hiulit/Murtop-Raspberry-Pi-Bartop-Arcade-Machine-Project/assets/images/GPIO-Adaftuit-retrogame.png

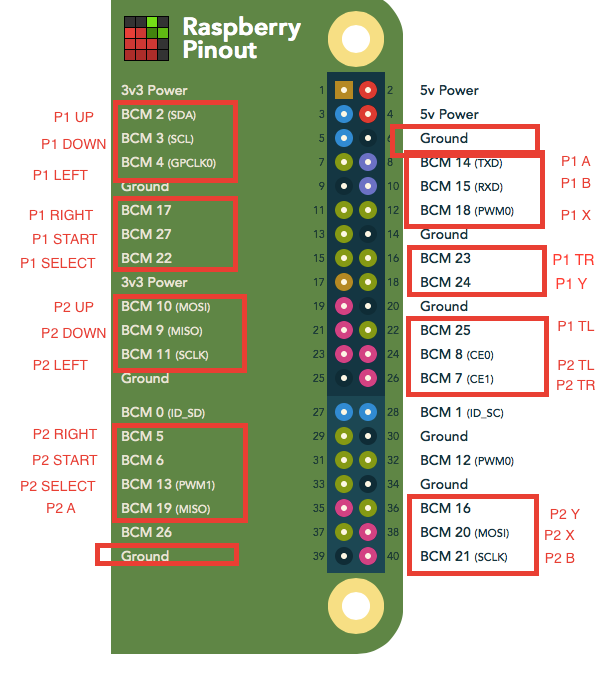
assets/images/GPIO-Adaftuit-retrogame.png
