hiulit/Murtop-Raspberry-Pi-Bartop-Arcade-Machine-Project/assets/images/wood-work-11.jpg

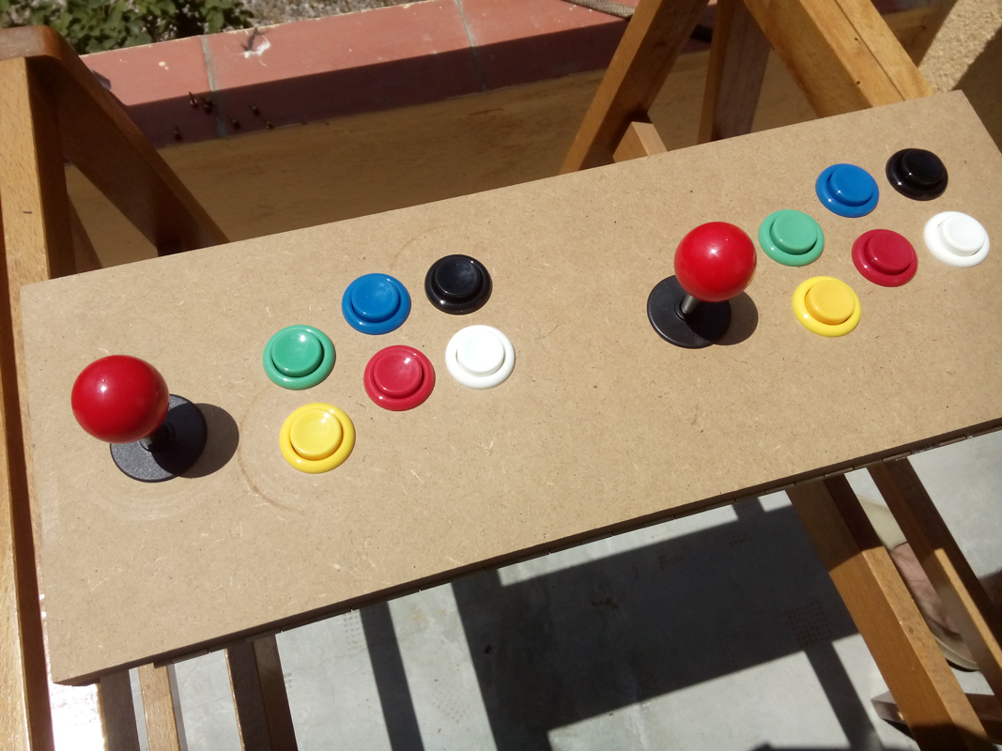
assets/images/wood-work-11.jpg
