hiulit/Murtop-Raspberry-Pi-Bartop-Arcade-Machine-Project/assets/images/wood-work-22.jpg

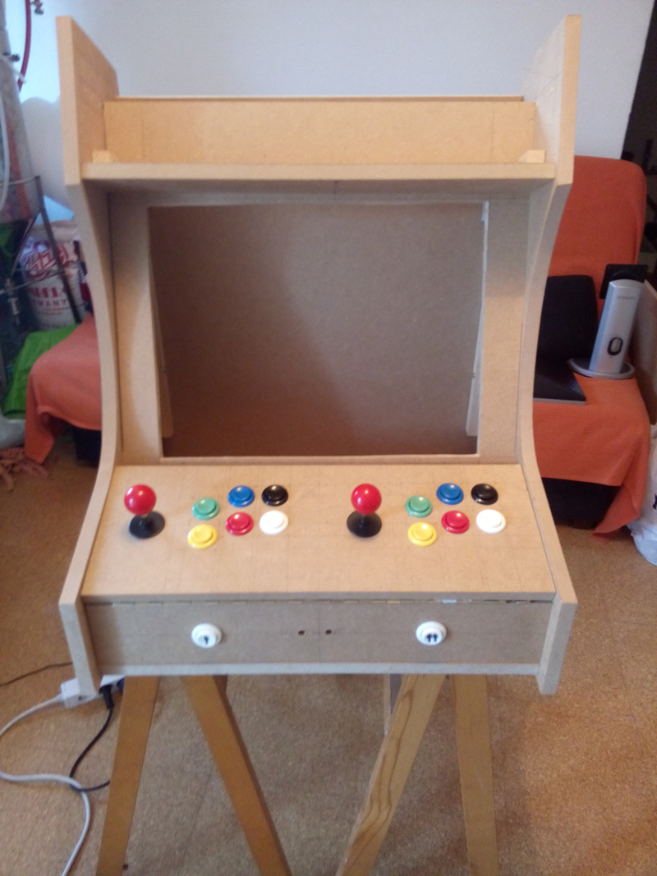
assets/images/wood-work-22.jpg
