hiulit/Murtop-Raspberry-Pi-Bartop-Arcade-Machine-Project/assets/images/wood-work-23.jpg

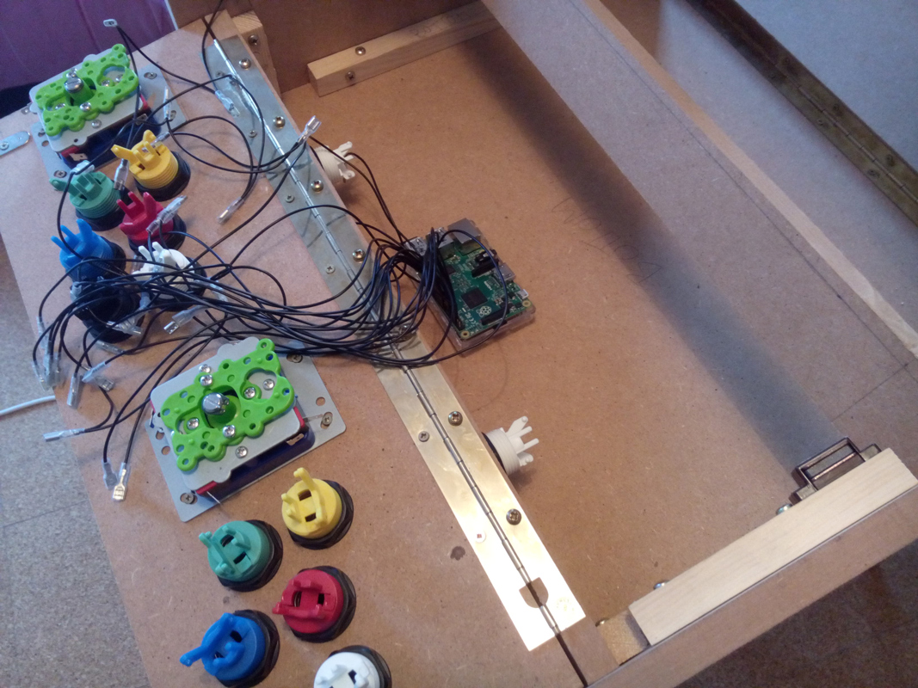
assets/images/wood-work-23.jpg
