hiulit/Murtop-Raspberry-Pi-Bartop-Arcade-Machine-Project/assets/images/wood-work-26.jpg

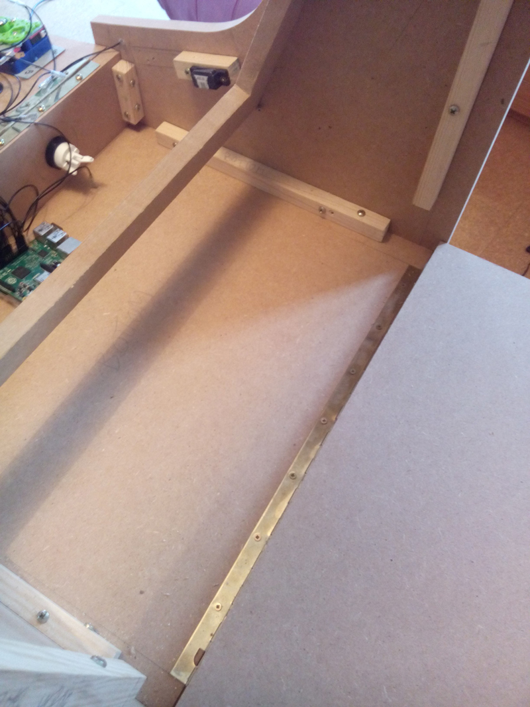
assets/images/wood-work-26.jpg
