hiulit/Murtop-Raspberry-Pi-Bartop-Arcade-Machine-Project/assets/images/wood-work-32.jpg

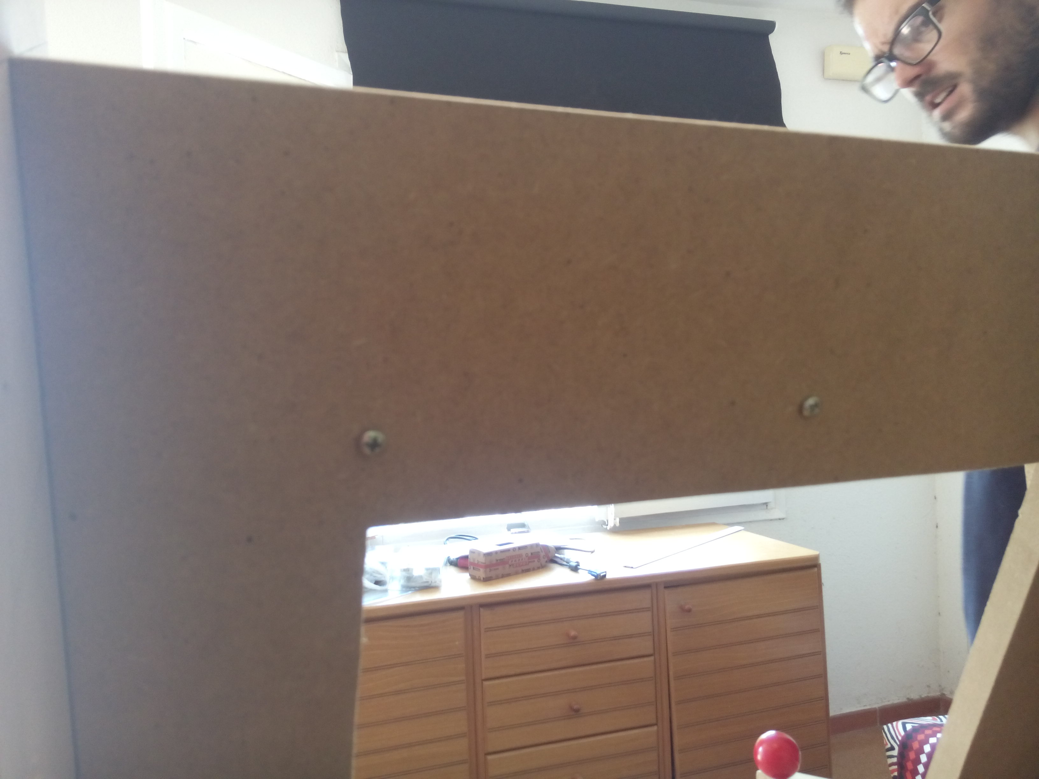
assets/images/wood-work-32.jpg
