hiulit/Murtop-Raspberry-Pi-Bartop-Arcade-Machine-Project/assets/images/wood-work-37.jpg

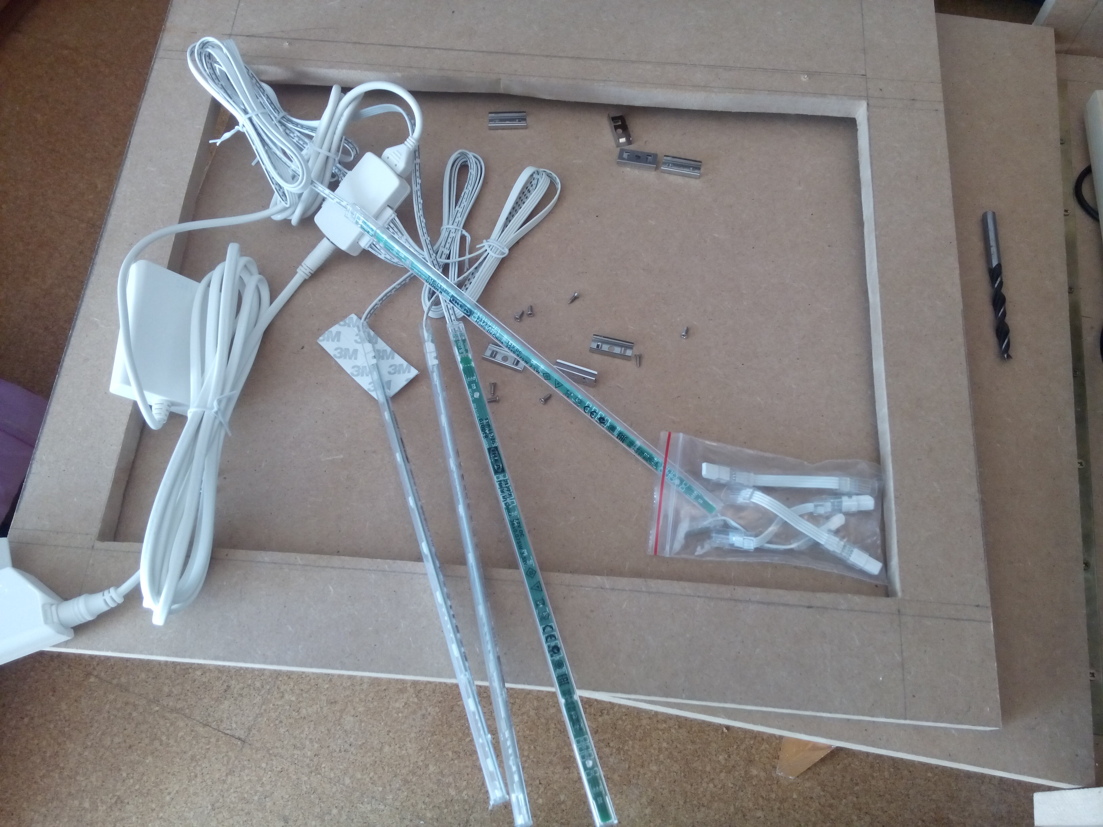
assets/images/wood-work-37.jpg
