hiulit/Murtop-Raspberry-Pi-Bartop-Arcade-Machine-Project/assets/images/wood-work-38.jpg

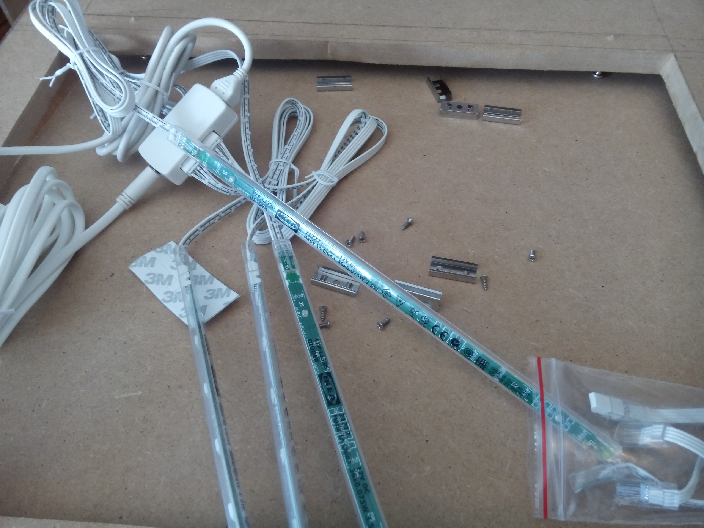
assets/images/wood-work-38.jpg
