hiulit/Murtop-Raspberry-Pi-Bartop-Arcade-Machine-Project/assets/images/wood-work-41.jpg

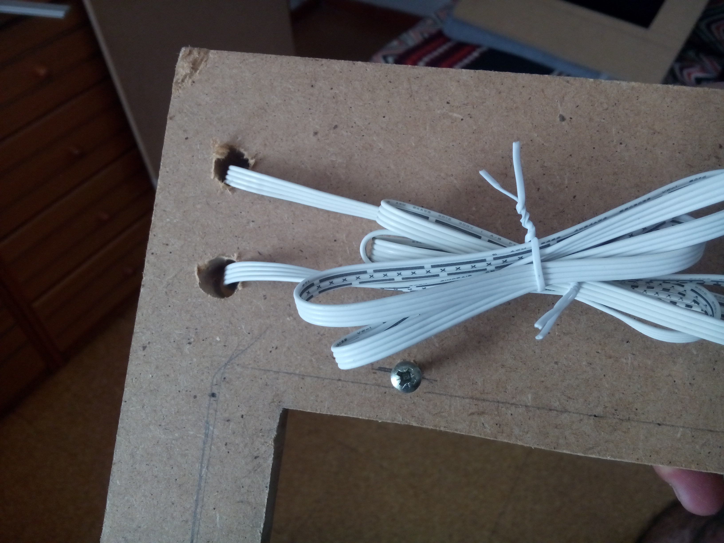
assets/images/wood-work-41.jpg
