hiulit/Murtop-Raspberry-Pi-Bartop-Arcade-Machine-Project/assets/images/wood-work-45.jpg

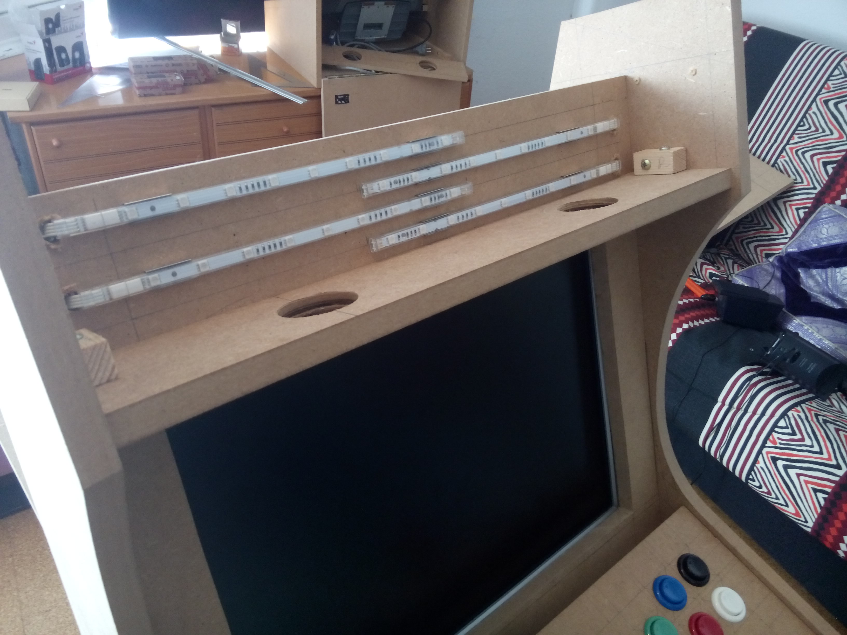
assets/images/wood-work-45.jpg
