hiulit/Murtop-Raspberry-Pi-Bartop-Arcade-Machine-Project/assets/images/wood-work-53.jpg

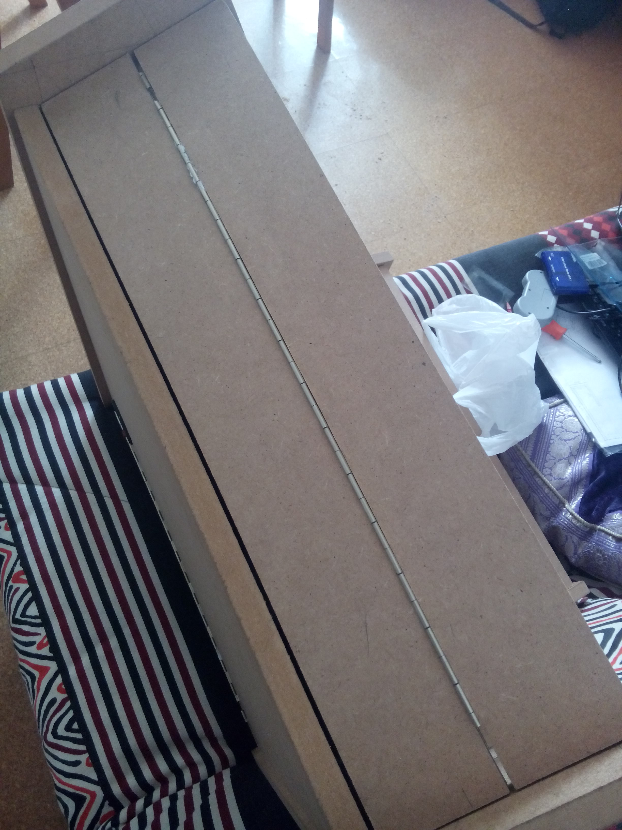
assets/images/wood-work-53.jpg
