hiulit/Murtop-Raspberry-Pi-Bartop-Arcade-Machine-Project/assets/images/wood-work-58.jpg

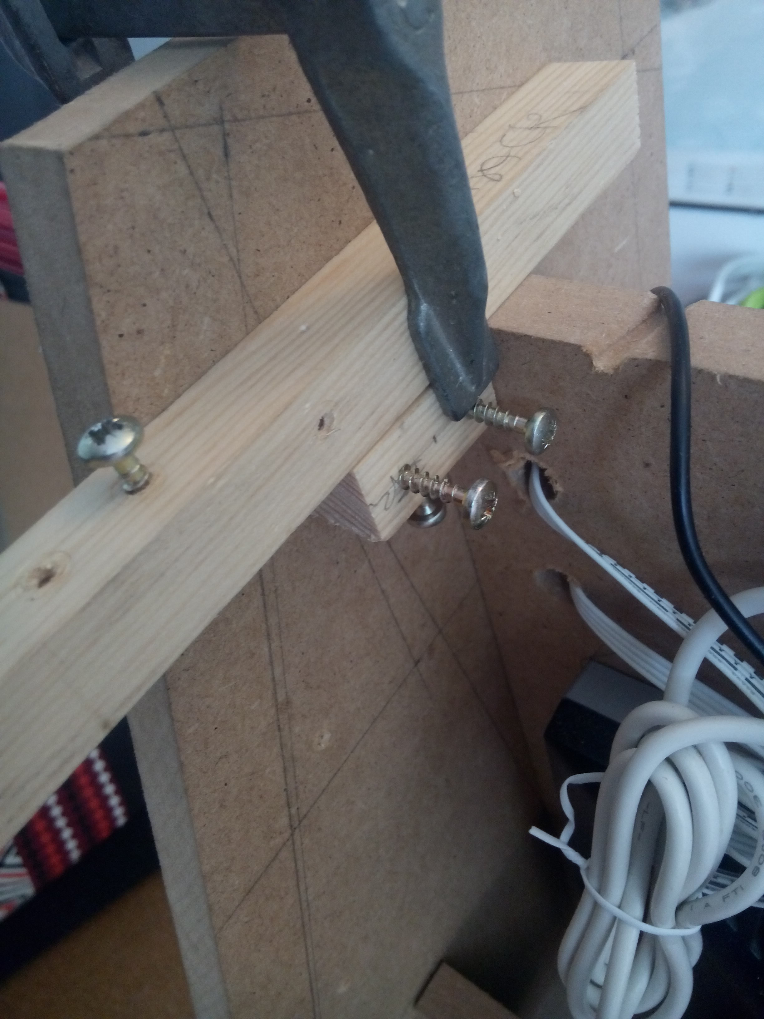
assets/images/wood-work-58.jpg
