hiulit/Murtop-Raspberry-Pi-Bartop-Arcade-Machine-Project/assets/images/wood-work-61.jpg

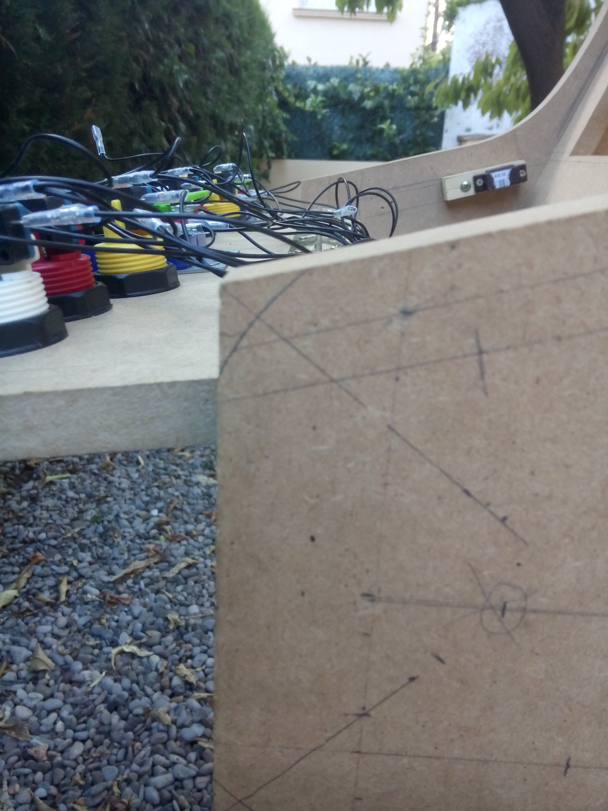
assets/images/wood-work-61.jpg
