hiulit/Murtop-Raspberry-Pi-Bartop-Arcade-Machine-Project/assets/images/wood-work-panting-01.jpg

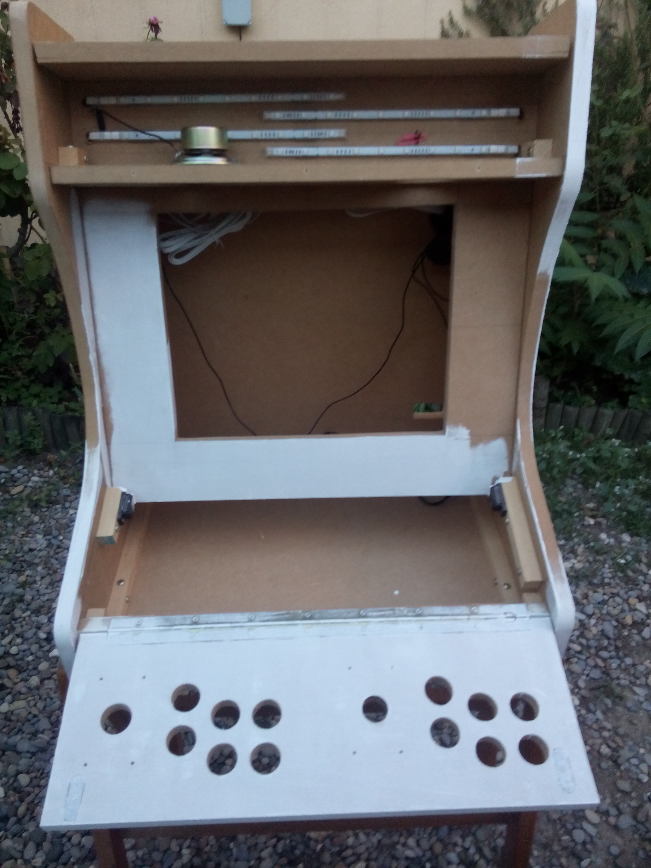
assets/images/wood-work-panting-01.jpg
