hiulit/Murtop-Raspberry-Pi-Bartop-Arcade-Machine-Project/assets/images/wood-work-panting-06.jpg

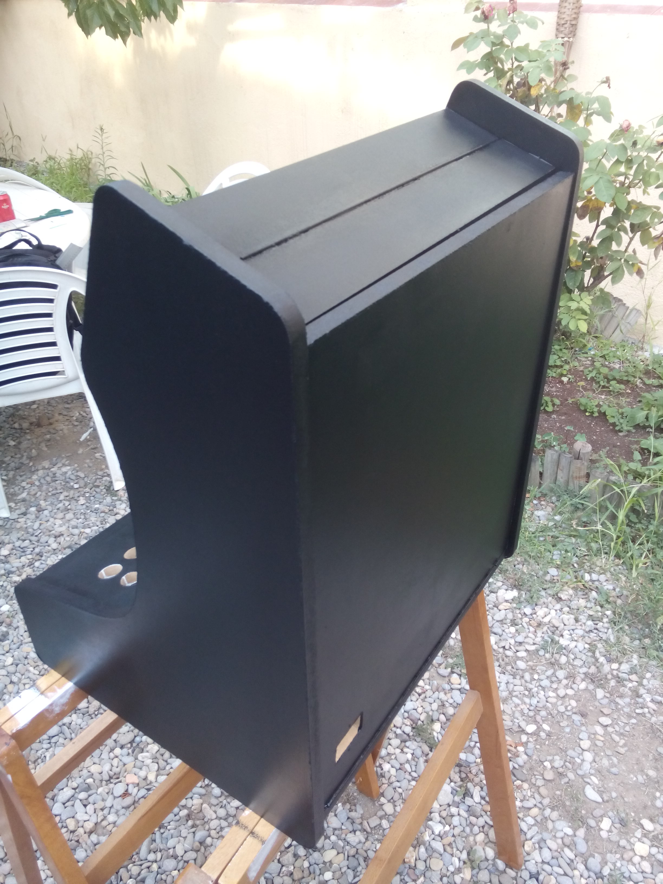
assets/images/wood-work-panting-06.jpg
