hiulit/Murtop-Raspberry-Pi-Bartop-Arcade-Machine-Project/assets/images/wood-work-wiring-02.jpg

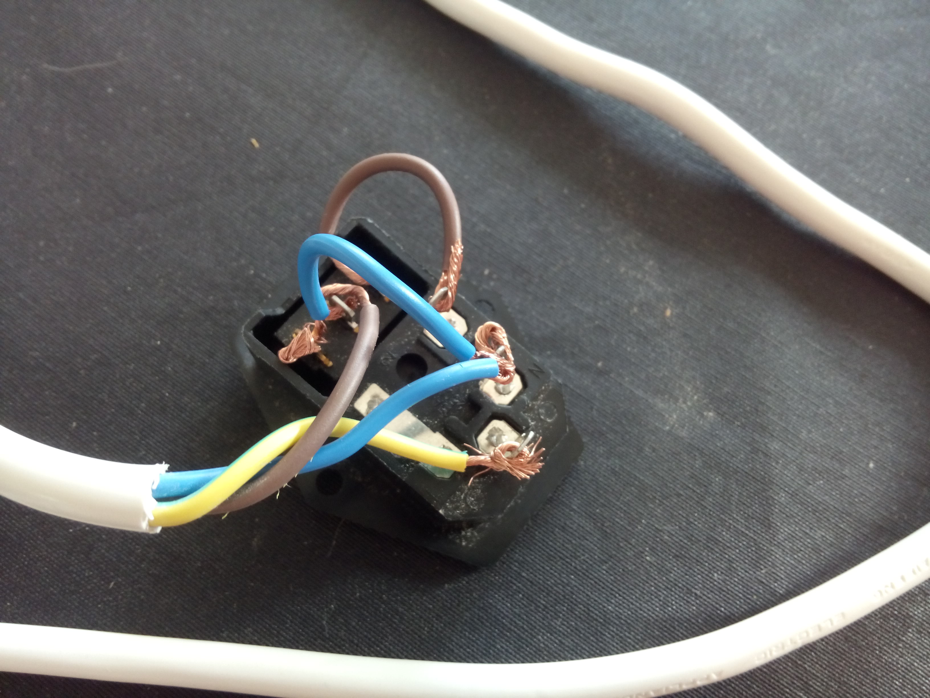
assets/images/wood-work-wiring-02.jpg
