hiulit/Murtop-Raspberry-Pi-Bartop-Arcade-Machine-Project/assets/images/wood-work-wiring-03.jpg

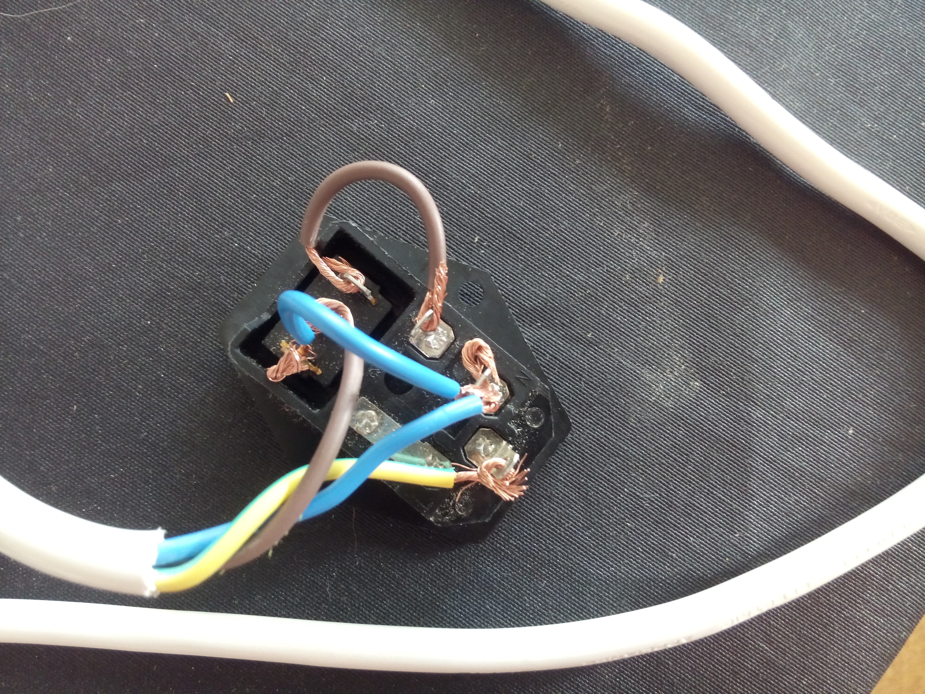
assets/images/wood-work-wiring-03.jpg
