hiulit/Murtop-Raspberry-Pi-Bartop-Arcade-Machine-Project/assets/images/wood-work-wiring-04.jpg

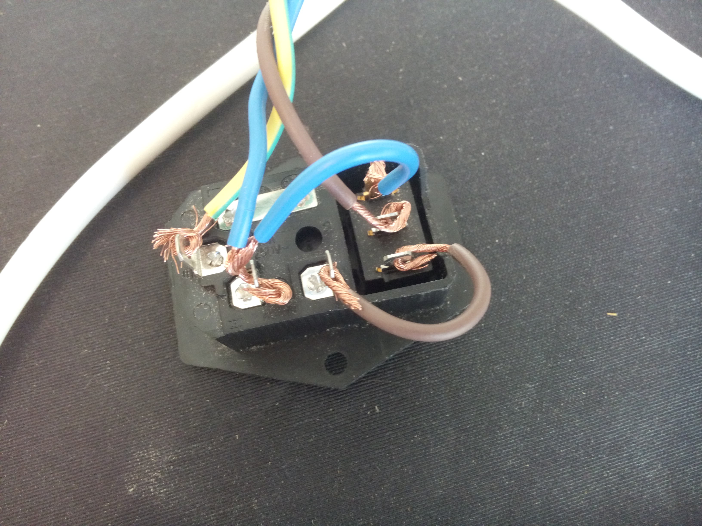
assets/images/wood-work-wiring-04.jpg
