hiulit/Murtop-Raspberry-Pi-Bartop-Arcade-Machine-Project/assets/images/wood-work-test-game-01.jpg

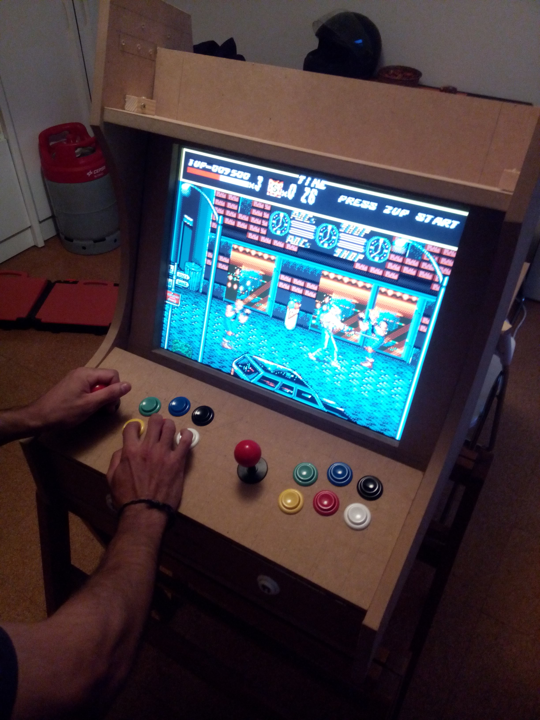
assets/images/wood-work-test-game-01.jpg
